MustBeArt/LAIR/hardware/graphics/LAIR32.png

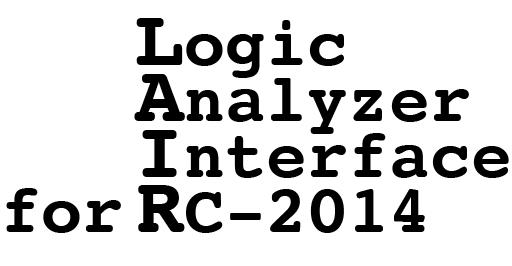
hardware/graphics/LAIR32.png
